surya-s-rai/Fluxon/Photos/Compartor Schema.png

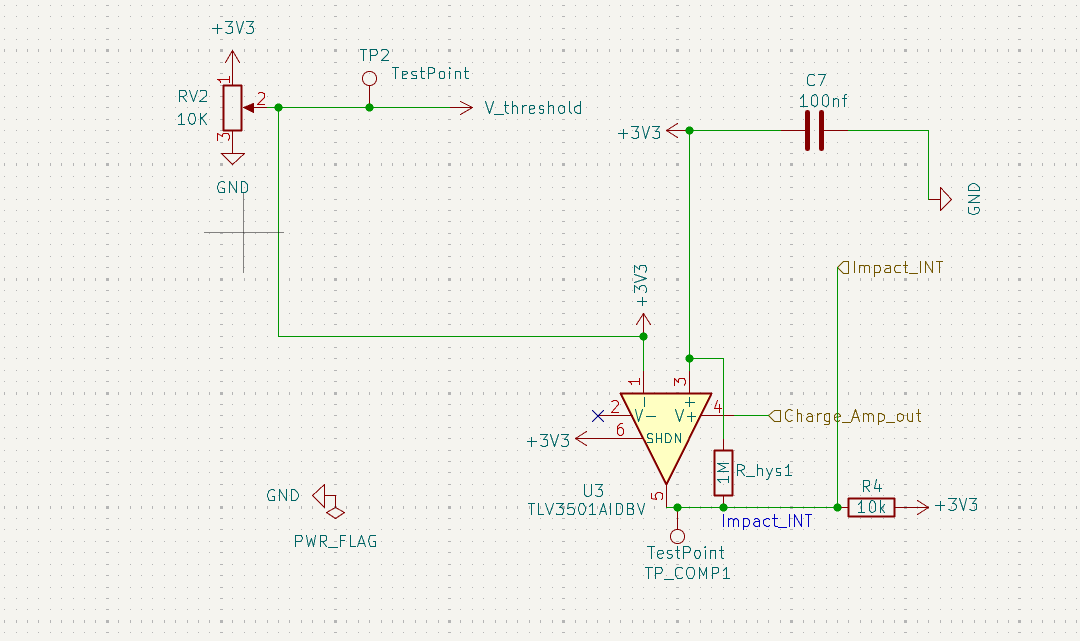
Photos/Compartor Schema.png
