surya-s-rai/Fluxon/Photos/Main Schema.png

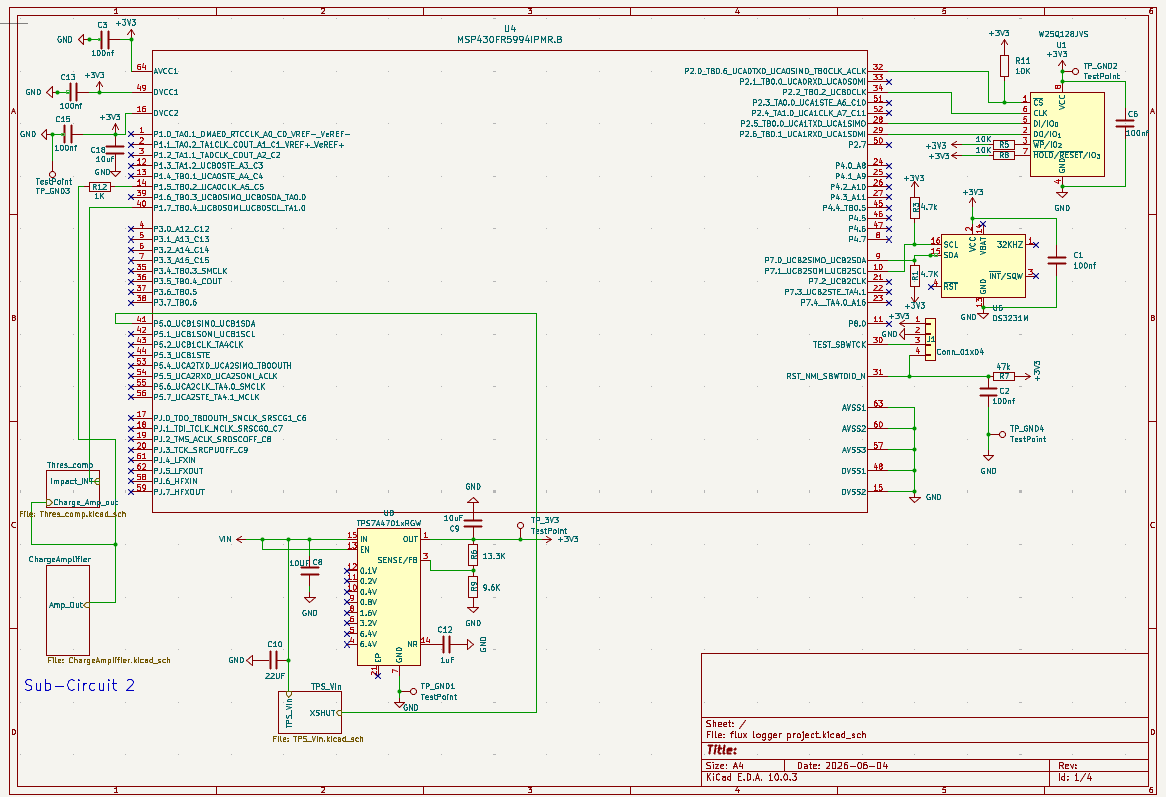
Photos/Main Schema.png
