surya-s-rai/Fluxon/Photos/solar Cell and Inductor Schema.png

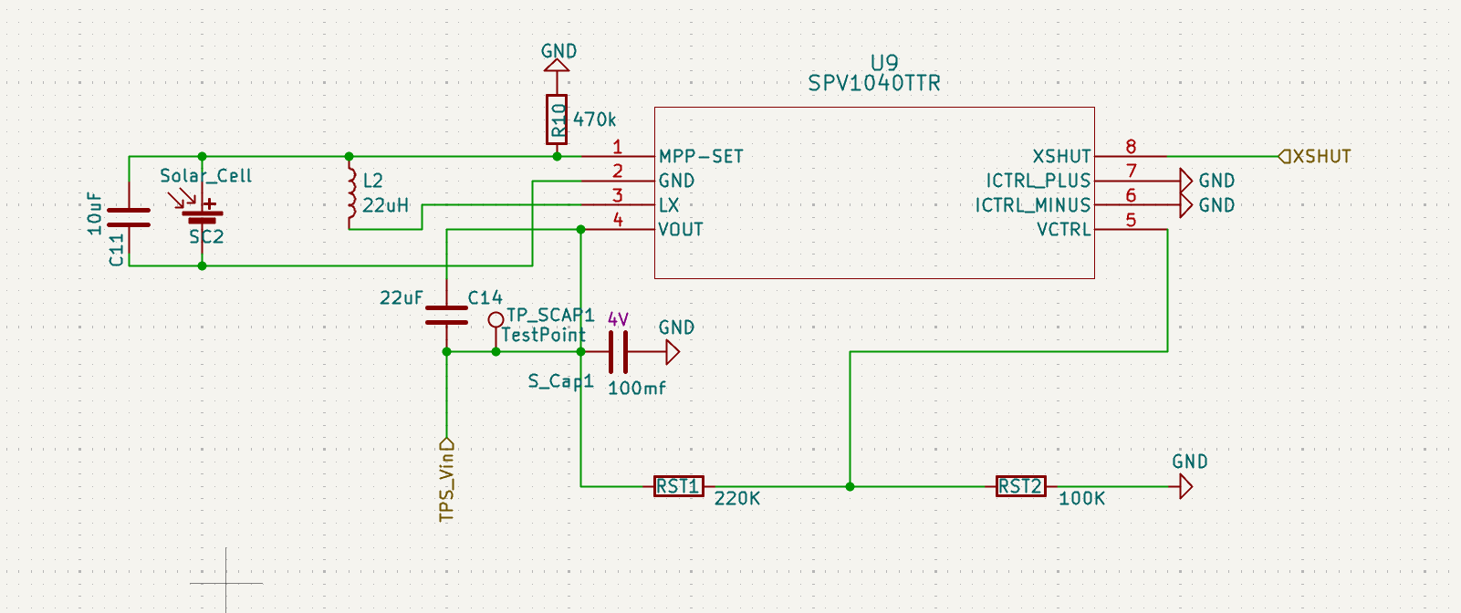
Photos/solar Cell and Inductor Schema.png
